liangaustin/Atmosphere/demo1/media/1786612738577.jpg

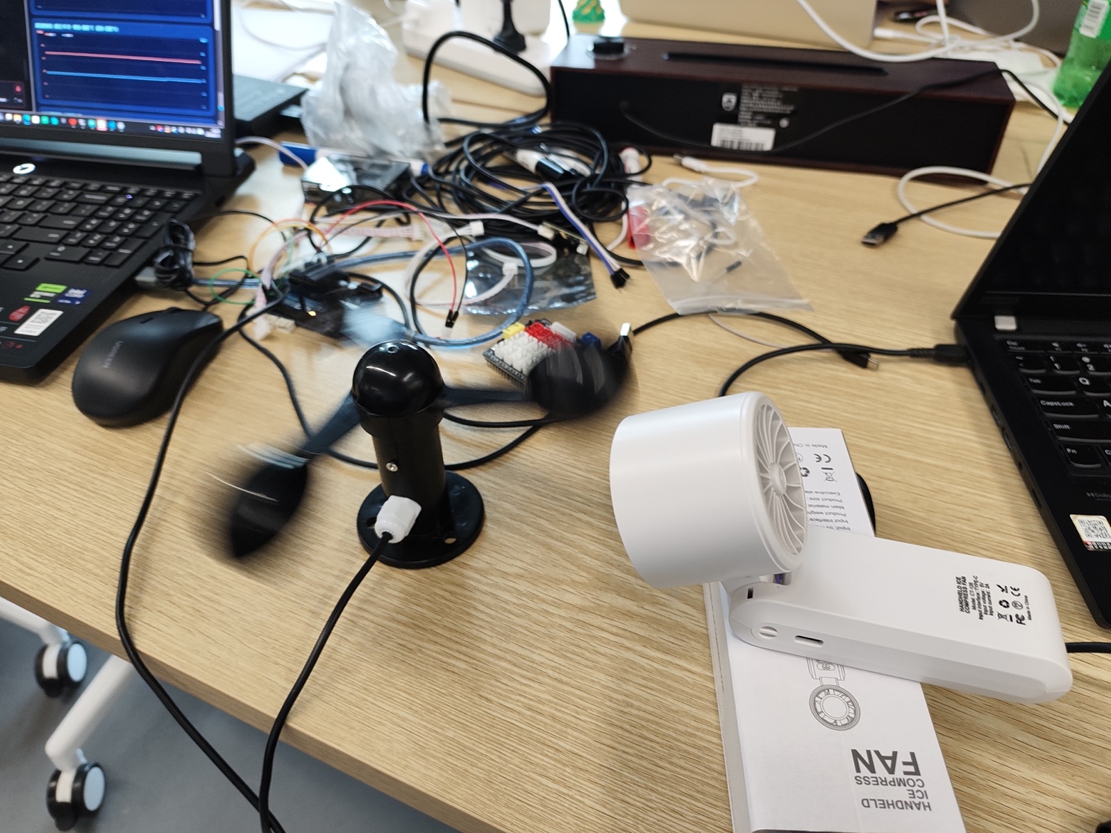
demo1/media/1786612738577.jpg
