liangaustin/Atmosphere/demo1/media/1786612738665.jpg

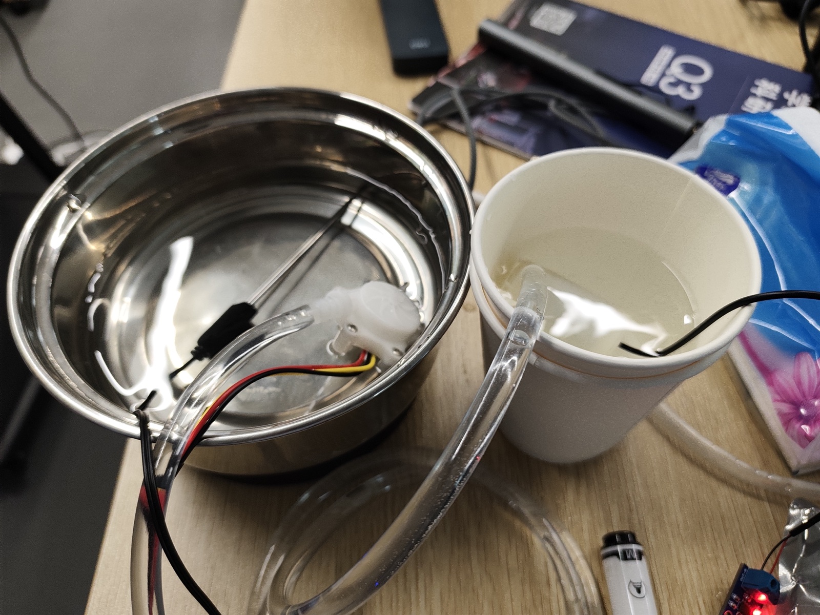
demo1/media/1786612738665.jpg
