liangaustin/Atmosphere/demo1/media/1786612738705.jpg

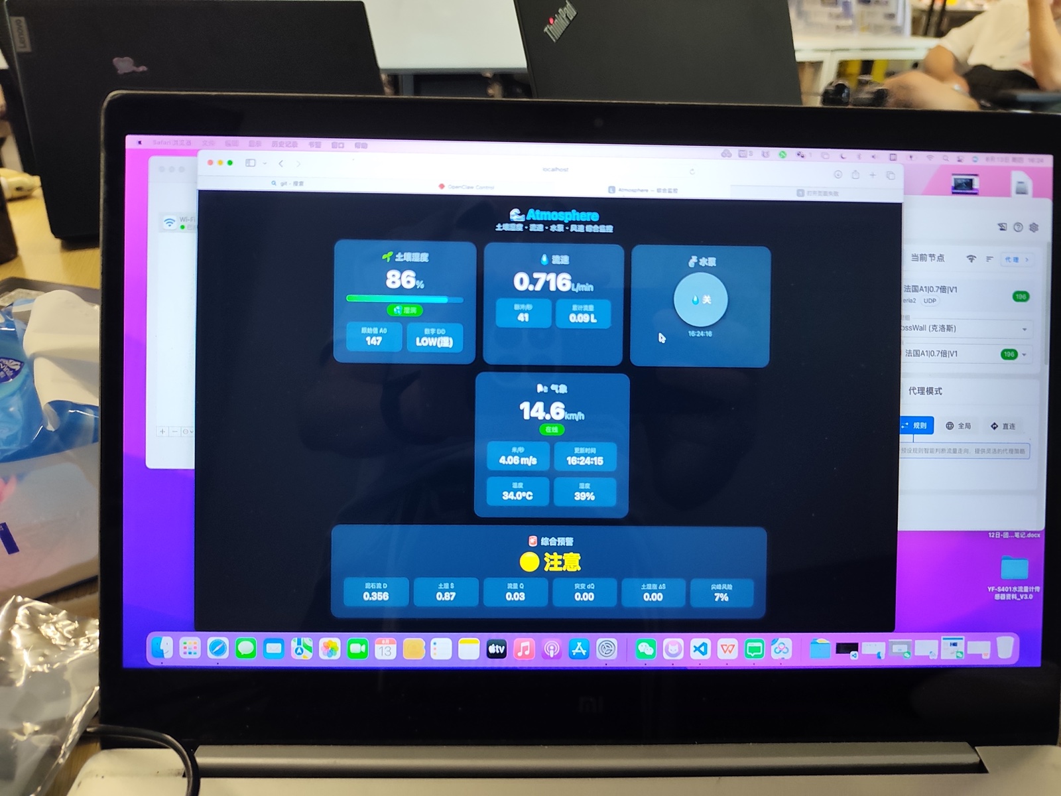
demo1/media/1786612738705.jpg
