liangaustin/Atmosphere/demo1/zh-CN/第二版算法部分/beta5/server.py

#!/usr/bin/env python3
"""Atmosphere - 综合监控：土壤湿度 + 流速 + 水泵控制"""
import json, time, http.server, threading, sys
import urllib.request
from collections import deque
import serial

SERIAL_PORT = "/dev/cu.usbserial-14120"
WIND_URL = "http://192.168.1.200:8001/wind"
WEB_PORT = 8080
latest = {
    "pump": 0, "soil_raw": 0, "soil_percent": -1, "soil_dry": False,
    "soil_connected": True, "flow_pulses": 0, "flow": 0.0, "total": 0.0,
    "wind_ms": 0.0, "wind_kmh": 0.0, "wind_time": "", "wind_connected": False,
    "temp": 0.0, "hum": 0.0, "dht_ok": False,
    "time": ""
}

ser = None
serial_lock = threading.Lock()

def read_serial():
    global latest, ser
    while True:
        try:
            with serial_lock:
                ser = serial.Serial(SERIAL_PORT, 115200, timeout=0.5)
                # 禁用 DTR/RTS，避免串口开关时触发 Arduino 自动复位
                ser.dtr = False
                ser.rts = False
            time.sleep(0.5)
            print(f"✅ 串口已连接: {SERIAL_PORT}", flush=True)
            last_read = time.time()
            while True:
                with serial_lock:
                    if ser is None:
                        raise TimeoutError("serial closed")
                    line = ser.readline()
                if line:
                    try:
                        data = json.loads(line.decode(errors='ignore').strip())
                        data["time"] = time.strftime("%H:%M:%S")
                        latest.update(data)
                        last_read = time.time()
                    except json.JSONDecodeError:
                        pass
                else:
                    # readline 超时返回空 → 累计 30 秒无数据才重连（减少复位频率）
                    if time.time() - last_read > 30:
                        print("⚠️ 30秒无数据，强制重连串口", flush=True)
                        raise TimeoutError("serial idle timeout")
        except Exception as e:
            print(f"❌ 串口错误，5秒后重连: {e}", flush=True)
            try:
                with serial_lock:
                    if ser:
                        ser.close()
            except Exception:
                pass
            ser = None
            time.sleep(5)

def lcd_sender():
    """每秒向 Arduino 下发 LCD 显示数据：D<风速km/h>,<预警等级>\n"""
    while True:
        try:
            with serial_lock:
                if ser is not None:
                    w = latest.get("wind_kmh", 0.0) or 0.0
                    lv = model.get("final_lv", 0)
                    ser.write(("D%.1f,%d\n" % (w, lv)).encode())
                    ser.flush()
        except Exception:
            pass
        time.sleep(1)

def fetch_wind():
    global latest
    last_ok = [0.0]
    while True:
        try:
            req = urllib.request.Request(WIND_URL, headers={'User-Agent': 'curl/7.64'})
            with urllib.request.urlopen(req, timeout=5) as r:
                d = json.loads(r.read().decode())
                latest["wind_ms"] = d.get("wind_ms", 0.0)
                latest["wind_kmh"] = d.get("wind_kmh", 0.0)
                latest["wind_time"] = d.get("time", "")
                # 温湿度：本地 DHT11 优先，无本地数据才用风速电脑的
                if not latest.get("dht_ok", False):
                    latest["temp"] = d.get("temp", 0.0)
                    latest["hum"] = d.get("hum", 0.0)
                last_ok[0] = time.time()
        except Exception:
            pass
        # 10 秒内有成功就算在线（容错对方时通时断）
        latest["wind_connected"] = (time.time() - last_ok[0]) < 10
        time.sleep(1)

# ══════════ 预警模型 ══════════
# 预警档位：0 正常 / 1 一级预警 / 2 二级预警 / 3 三级预警（三级最严重）
LV_TEXT = ["🟢 正常", "🟡 一级预警", "🟠 二级预警", "🔴 三级预警"]

# 泥石流模型标定参数（v2：对齐 YF-S401 实测量程）
Q_MAX = 3.0    # 满槽流量 L/min（实测新泵最大 ~1.7，留余量 3）
DQ_MAX = 0.5   # 流量变化率上限 L/min/s（实测秒级跳变 ~0.3）
DS_MAX = 15.0  # 土壤10分钟变化上限 %

flow_hist = deque(maxlen=300)   # 5分钟流量历史（每秒一点）
soil_hist = deque(maxlen=600)   # 10分钟湿度历史（每秒一点）
wind_hist = deque(maxlen=300)   # 5分钟风速历史（每秒一点）
hist_lock = threading.Lock()

# ── 滑动基准（24小时窗口，每分钟一点，自适应地区气候）──
BASE_LEN = 1440        # 24h × 60min
BASE_MIN = 15          # 收集 15 分钟数据即启用滑动基准（v2 调整：120→15，更快自适应）
flow_base = deque(maxlen=BASE_LEN)
soil_base = deque(maxlen=BASE_LEN)
spike_base = deque(maxlen=BASE_LEN)   # 尖峰基准（流量秒级变化率）
base_last = [0.0]      # 上次基准采样时间

def pct(data, p):
    """排序后取第 p 百分位（0-100）"""
    if not data:
        return None
    s = sorted(data)
    idx = int(len(s) * p / 100.0)
    idx = max(0, min(len(s) - 1, idx))
    return s[idx]

def sliding_norm(v, base):
    """把当前值映射到该地 [P10, P95] 区间的 0~1 相对偏离；数据不足返回 None"""
    if len(base) < BASE_MIN:
        return None
    p10 = pct(base, 10)
    p95 = pct(base, 95)
    if p95 - p10 < 1e-6:
        return None
    return max(0.0, min(1.0, (v - p10) / (p95 - p10)))

# 滞回保持：各等级最短保持秒数（防抖，避免预警闪一下就恢复）
HOLD_SEC = {1: 10, 2: 15, 3: 20}
_lv_hold_until = [0.0, 0.0, 0.0, 0.0]
_cur_lv = [0]

model = {
    "debris_D": 0.0, "debris_lv": 0, "debris_lv_text": LV_TEXT[0],
    "Sn": 0.0, "Qn": 0.0, "dQn": 0.0, "dSn": 0.0,
    "spike": 0.0, "spike_risk": 0.0,
    "final_lv": 0, "final_lv_text": LV_TEXT[0],
}

def rising_5min():
    """流量是否连续5分钟上升（5段60秒窗口，≥4段上升判定为持续上涨）"""
    if len(flow_hist) < 300:
        return False
    seg = []
    for i in range(5):
        vals = [flow_hist[j][1] for j in range(-300 + i * 60, -240 + i * 60)]
        seg.append(sum(vals) / 60.0)
    up = sum(1 for i in range(4) if seg[i + 1] > seg[i])
    return up >= 4

def model_loop():
    global model
    while True:
        try:
            with hist_lock:
                t = time.time()
                flow = latest.get("flow", 0.0)
                soil = latest.get("soil_percent", -1)
                if soil < 0:
                    soil = 0
                flow_hist.append((t, flow))
                soil_hist.append((t, soil))
                wind_hist.append((t, latest.get("wind_kmh", 0.0)))

                # 每分钟采样到 24h 滑动基准窗口
                if t - base_last[0] >= 60:
                    base_last[0] = t
                    flow_base.append(flow)
                    soil_base.append(soil)
                    _spk = flow_hist[-1][1] - flow_hist[-2][1] if len(flow_hist) >= 2 else 0.0
                    spike_base.append(max(0.0, _spk))

                # ── 泥石流四因子归一化（滑动基准自适应，数据不足回退绝对值）──
                Sn = sliding_norm(soil, soil_base)
                if Sn is None:
                    Sn = soil / 100.0
                Qn = sliding_norm(flow, flow_base)
                if Qn is None:
                    Qn = min(flow / Q_MAX, 1.0)
                dq = (flow_hist[-1][1] - flow_hist[-60][1]) / 60.0 if len(flow_hist) >= 60 else 0.0
                dqn = min(abs(dq) / DQ_MAX, 1.0)
                ds = 0.0
                if len(soil_hist) >= 600:
                    ds = soil_hist[-1][1] - soil_hist[-600][1]
                    if ds < 0:
                        ds = 0
                dsn = min(ds / DS_MAX, 1.0)

                # 综合危险指数 D = 0.30S̄ + 0.35Q̄ + 0.20(dQ/dt)̄ + 0.15(ΔS)̄
                # v1 调整：土壤 0.40→0.30（土湿易饱和顶分），流量升为最高权重（山洪更关键）
                D = 0.30 * Sn + 0.35 * Qn + 0.20 * dqn + 0.15 * dsn

                # ── 山洪路径（独立于土壤门槛：流量水平 + 流量突变）──
                # F = 0.6Q̄ + 0.4dQ̄，模拟曼宁公式缺水位时的流量近似
                F = 0.6 * Qn + 0.4 * dqn
                flood_lv = 0
                if F >= 0.75: flood_lv = 3
                elif F >= 0.55: flood_lv = 2
                elif F >= 0.45: flood_lv = 1

                # ── 泥石流分级（特殊规则优先）──
                # 土壤"高湿"判定：优先滑动基准 P90，数据不足回退绝对 60%
                _sp90 = pct(soil_base, 90)
                soil_high = (soil > _sp90) if _sp90 is not None else (soil >= 60)

                debris_lv = 0
                # 门槛：土壤未饱和（<60%）时泥石流起不来，直接安全，不参与 D 分级
                if soil >= 60:
                    if soil_high and dq > 0 and rising_5min():
                        debris_lv = 3
                    elif soil_high and Qn >= 0.70:
                        debris_lv = 2
                    if ds >= 20 and debris_lv < 1:
                        debris_lv = 1
                    if debris_lv == 0:
                        if D >= 0.75:
                            debris_lv = 3
                        elif D >= 0.55:
                            debris_lv = 2
                        elif D >= 0.45:   # 0.30→0.45，土壤湿度单独(≤0.40)不再触发三级
                            debris_lv = 1

                # ── 山洪尖峰（30%分量，用流量秒级变化率近似；曼宁需水位暂缺）──
                spike = max(0.0, flow_hist[-1][1] - flow_hist[-2][1]) if len(flow_hist) >= 2 else 0.0
                # 尖峰按滑动基准自适应：对比当地历史流量变化率分布，超 P95 才算高风险
                spike_risk = sliding_norm(spike, spike_base)
                if spike_risk is None:
                    spike_risk = min(spike / 0.5, 1.0)  # 基准不足回退：实测秒级变化率 ~0.3，0.5 为高值

                # ── 风速风险（独立因子；强风 = 强对流前兆，山洪诱因）──
                w = latest.get("wind_kmh", 0.0)
                wind_risk = min(w / 40.0, 1.0)
                wind_lv = 0
                if w >= 60: wind_lv = 3
                elif w >= 40: wind_lv = 2
                elif w >= 25: wind_lv = 1
                # 风速突变：60 秒内涨 ≥12 km/h → 升一级
                wind_surge = len(wind_hist) >= 60 and (w - wind_hist[-60][1]) >= 12
                # 土壤秒级突变：5 秒内涨 ≥20% → 一级（饱和渗流信号）
                soil_surge = len(soil_hist) >= 5 and (soil - soil_hist[-5][1]) >= 20
                # 流量尖峰等级（spike_risk 满 1.0 = 超当地 P95）
                spike_lv = 0
                if spike_risk >= 1.0: spike_lv = 2
                elif spike_risk >= 0.8: spike_lv = 1
                # 突变合并
                surge_lv = 1 if (wind_surge or soil_surge) else 0

                # 土壤持续高饱和：≥85% 或超当地 P90 → 至少一级（不依赖流量，土体饱和本身就是危险）
                soil_sat_lv = 1 if (soil >= 85 or (_sp90 is not None and soil > _sp90)) else 0

                # 最终等级 = 各因子取最高（泥石流 / 山洪 / 风速 / 尖峰 / 突变 / 土壤饱和）
                final_raw = max(debris_lv, flood_lv, wind_lv, spike_lv, surge_lv, soil_sat_lv)
                # 滞回：升级立即生效并保持；降级需超过保持时间
                tnow = time.time()
                if final_raw >= _cur_lv[0]:
                    _cur_lv[0] = final_raw
                    _lv_hold_until[final_raw] = tnow + HOLD_SEC.get(final_raw, 10)
                elif tnow >= _lv_hold_until[_cur_lv[0]]:
                    _cur_lv[0] = final_raw
                final_lv = _cur_lv[0]

                model.update({
                    "debris_D": round(D, 3), "debris_lv": debris_lv,
                    "debris_lv_text": LV_TEXT[debris_lv],
                    "flood_F": round(F, 3), "flood_lv": flood_lv,
                    "Sn": round(Sn, 3), "Qn": round(Qn, 3),
                    "dQn": round(dqn, 3), "dSn": round(dsn, 3),
                    "spike": round(spike, 3), "spike_risk": round(spike_risk, 3),
                    "wind_risk": round(wind_risk, 3), "wind_lv": wind_lv,
                    "final_lv": final_lv, "final_lv_text": LV_TEXT[final_lv],
                    "baseline_ready": len(soil_base) >= BASE_MIN,
                    "soil_p90": round(_sp90, 1) if _sp90 is not None else -1,
                })
        except Exception as e:
            print(f"模型计算错误: {e}", flush=True)
        time.sleep(1)

HTML = """<!DOCTYPE html>
<html lang="zh-CN">
<head>
<meta charset="UTF-8">
<meta name="viewport" content="width=device-width, initial-scale=1.0">
<title>Atmosphere — 综合监控</title>
<style>
*{margin:0;padding:0;box-sizing:border-box}
body{font-family:-apple-system,system-ui,sans-serif;background:#0b1218;color:#e0e0e0;
  min-height:100vh;padding:24px;display:flex;flex-direction:column;align-items:center}
h1{font-size:1.6em;color:#4fc3f7;margin-bottom:4px}
.sub{color:#78909c;margin-bottom:24px;font-size:.85em}
.grid{display:flex;gap:16px;flex-wrap:wrap;justify-content:space-evenly;max-width:1200px;width:100%;margin-bottom:20px}
.card.full{flex-basis:100%;max-width:100%}
.card{background:#1a2a36;border-radius:18px;padding:18px 20px;flex:1;min-width:230px;max-width:270px;text-align:center}
.card h2{font-size:.95em;color:#90a4ae;font-weight:600;margin-bottom:12px;letter-spacing:.5px}
.big{font-size:2.2em;font-weight:800;line-height:1;margin:6px 0}
.unit{font-size:.4em;color:#78909c;font-weight:400}
/* 湿度进度条 */
.bar{height:10px;background:#1e3a4a;border-radius:6px;overflow:hidden;margin:14px 0 6px}
.bar .fill{height:100%;background:linear-gradient(90deg,#43a047,#4fc3f7);border-radius:6px;transition:width .4s}
.tag{font-size:.8em;padding:4px 12px;border-radius:14px;display:inline-block}
.tag.wet{background:#1b5e20;color:#81c784}
.tag.dry{background:#5d4037;color:#ffab91}
.tag.disconn{background:#b71c1c;color:#ffcdd2}
/* 水泵开关 */
.switch{width:92px;height:92px;border-radius:50%;border:none;font-size:.95em;font-weight:700;
  cursor:pointer;margin:8px auto 6px;display:block;transition:all .2s;color:#fff}
.switch.off{background:#455a64;box-shadow:0 4px 12px rgba(0,0,0,.4)}
.switch.on{background:#2e7d32;box-shadow:0 4px 20px rgba(46,125,50,.6)}
.switch:active{transform:scale(.94)}
/* 曲线区 */
.legend{display:flex;gap:16px;justify-content:center;font-size:.75em;color:#90a4ae;margin-top:6px;flex-wrap:wrap}
.legend span{display:inline-flex;align-items:center;gap:5px}
.legend b{color:#e0e0e0}
.dot{width:12px;height:3px;border-radius:2px;display:inline-block}
canvas{width:100%;display:block;aspect-ratio:14/3}
.row{display:flex;gap:10px;margin-top:14px}
.mini{flex:1;background:#1e3a4a;border-radius:10px;padding:10px}
.mini .lb{font-size:.68em;color:#78909c}
.mini .vl{font-size:1.15em;font-weight:600;margin-top:4px}
.time{color:#546e7a;font-size:.75em;margin-top:20px}
</style>
</head>
<body>
<h1>🌊 Atmosphere</h1>
<div class="sub">土壤湿度 · 流速 · 水泵 · 风速 综合监控</div>

<div class="grid">
  <!-- 土壤湿度卡片 -->
  <div class="card">
    <h2>🌱 土壤湿度</h2>
    <div class="big"><span id="soil">--</span><span class="unit">%</span></div>
    <div class="bar"><div class="fill" id="soilBar" style="width:0%"></div></div>
    <span class="tag disconn" id="soilTag">--</span>
    <div class="row">
      <div class="mini"><div class="lb">原始值 A0</div><div class="vl" id="soilRaw">--</div></div>
      <div class="mini"><div class="lb">数字 DO</div><div class="vl" id="soilDO">--</div></div>
    </div>
  </div>

  <!-- 流速卡片 -->
  <div class="card">
    <h2>💧 流速</h2>
    <div class="big"><span id="flow">0.000</span><span class="unit">L/min</span></div>
    <div class="row">
      <div class="mini"><div class="lb">脉冲/秒</div><div class="vl" id="pulses">--</div></div>
      <div class="mini"><div class="lb">累计流量</div><div class="vl" id="total">--</div></div>
    </div>
  </div>

  <!-- 水泵卡片 -->
  <div class="card">
    <h2>🚰 水泵</h2>
    <button class="switch off" id="pumpBtn">💧 关</button>
    <div class="row" style="margin-top:14px">
      <div class="mini" style="flex:1"><div class="lb">速度</div><div class="vl" id="speedLbl">0%</div></div>
      <div class="mini" style="flex:1"><div class="lb">整机功率</div><div class="vl" id="powerLbl">0.40 W</div></div>
    </div>
    <input type="range" id="speedSlider" min="0" max="100" value="0"
      style="width:100%;margin-top:12px;accent-color:#2e7d32">
    <div class="time" id="time" style="margin-top:8px">--</div>
  </div>
  <!-- 气象卡片 -->
  <div class="card">
    <h2>🌬️ 气象</h2>
    <div class="big"><span id="wind">--</span><span class="unit">km/h</span></div>
    <span class="tag disconn" id="windTag">--</span>
    <div class="row">
      <div class="mini"><div class="lb">米/秒</div><div class="vl" id="windMs">--</div></div>
      <div class="mini"><div class="lb">更新时间</div><div class="vl" id="windTime">--</div></div>
    </div>
    <div class="row">
      <div class="mini"><div class="lb">温度</div><div class="vl" id="tempV">--</div></div>
      <div class="mini"><div class="lb">湿度</div><div class="vl" id="humV">--</div></div>
    </div>
  </div>
</div>

<div class="grid">
  <!-- 曲线卡片 -->
  <div class="card full">
    <h2>📈 实时曲线（温度 · 湿度 · 风速）</h2>
    <canvas id="mainChart"></canvas>
    <div class="legend"><span><i class="dot" style="background:#ef5350"></i>温度 <b id="curTemp">--</b>℃</span><span><i class="dot" style="background:#42a5f5"></i>湿度 <b id="curHum">--</b>%</span><span><i class="dot" style="background:#66bb6a"></i>风速 <b id="curWind">--</b>km/h</span></div>
  </div>
</div>

<div class="grid">
  <!-- 预警卡片 -->
  <div class="card full">
    <h2>🚨 综合预警</h2>
    <div class="big" id="alertLv" style="font-size:1.8em">--</div>
    <div class="row" style="flex-wrap:wrap;justify-content:center">
      <div class="mini"><div class="lb">泥石流 D</div><div class="vl" id="debrisD">--</div></div>
      <div class="mini"><div class="lb">土湿 S̄</div><div class="vl" id="fSn">--</div></div>
      <div class="mini"><div class="lb">流量 Q̄</div><div class="vl" id="fQn">--</div></div>
      <div class="mini"><div class="lb">突变 dQ̄</div><div class="vl" id="fdQn">--</div></div>
      <div class="mini"><div class="lb">土湿涨 ΔS̄</div><div class="vl" id="fdSn">--</div></div>
      <div class="mini"><div class="lb">尖峰风险</div><div class="vl" id="spikeRisk">--</div></div>
      <div class="mini"><div class="lb">山洪 F</div><div class="vl" id="floodF">--</div></div>
      <div class="mini"><div class="lb">风速风险</div><div class="vl" id="windRisk">--</div></div>
    </div>
  </div>
</div>

<script>
let pumpState = 0;
let pumpSpeedPct = 0;
const MAX_POINTS = 600;   // 5 分钟曲线（500ms 一点）
let history = [];

function drawLineChart(canvas, series){
  const dpr = window.devicePixelRatio || 1;
  const w = canvas.clientWidth, h = canvas.clientHeight;
  if(!w || !h) return;
  canvas.width = w * dpr; canvas.height = h * dpr;
  const ctx = canvas.getContext('2d');
  ctx.setTransform(dpr, 0, 0, dpr, 0, 0);
  ctx.clearRect(0, 0, w, h);
  const padL = 34, padR = 34, padT = 8, padB = 16;
  const gw = w - padL - padR, gh = h - padT - padB;
  // 网格 + 刻度（left 系列左轴，right 系列右轴）
  ctx.strokeStyle = '#1e3a4a'; ctx.lineWidth = 1;
  ctx.fillStyle = '#78909c'; ctx.font = '9px sans-serif';
  for(let i = 0; i <= 4; i++){
    const y = padT + gh * i / 4;
    ctx.beginPath(); ctx.moveTo(padL, y); ctx.lineTo(w - padR, y); ctx.stroke();
    const left = series.find(s => s.side === 'left'), right = series.find(s => s.side === 'right');
    if(left){
      ctx.textAlign = 'right';
      const v = left.yMax - (left.yMax - left.yMin) * i / 4;
      ctx.fillText(v.toFixed(1), padL - 4, y + 3);
    }
    if(right){
      ctx.textAlign = 'left';
      const v = right.yMax - (right.yMax - right.yMin) * i / 4;
      ctx.fillText(v.toFixed(0), w - padR + 4, y + 3);
    }
  }
  // 右侧时间
  ctx.textAlign = 'right'; ctx.fillStyle = '#546e7a';
  const now = new Date();
  const ts = [now.getHours(), now.getMinutes(), now.getSeconds()].map(x => String(x).padStart(2, '0')).join(':');
  ctx.fillText(ts, w - 2, h - 2);
  // 曲线（数据不满 600 点时拉伸铺满全宽；满后固定窗口滚动）
  for(const s of series){
    ctx.strokeStyle = s.color; ctx.lineWidth = 1.8;
    ctx.beginPath(); let started = false;
    const n = s.data.length;
    for(let i = 0; i < n; i++){
      const v = s.data[i];
      if(v === null || v === undefined){ started = false; continue; }
      let x;
      if(n <= MAX_POINTS){
        x = padL + gw * (n > 1 ? i / (n - 1) : 0);        // 数据少 → 铺满
      } else {
        x = padL + gw * (i - (n - MAX_POINTS)) / (MAX_POINTS - 1);  // 满窗 → 滚动
      }
      const y = padT + gh * (1 - (v - s.yMin) / (s.yMax - s.yMin));
      if(!started){ ctx.moveTo(x, y); started = true; }
      else ctx.lineTo(x, y);
    }
    ctx.stroke();
  }
}

function drawCharts(){
  const temps = history.map(p => p.temp), hums = history.map(p => p.hum), winds = history.map(p => p.wind);
  // 温度动态范围（左轴）
  const tvals = temps.filter(v => v !== null && v !== undefined);
  let tMin = 15, tMax = 35;
  if(tvals.length){ tMin = Math.min(...tvals); tMax = Math.max(...tvals); }
  tMin -= 2; tMax += 2;
  if(tMax - tMin < 4) tMax = tMin + 4;
  // 风速动态范围（自身归一化，无刻度）
  const wvals = winds.filter(v => v !== null && v !== undefined);
  let wMax = 20;
  if(wvals.length) wMax = Math.max(wMax, Math.ceil(Math.max(...wvals) * 1.2 / 10) * 10);
  drawLineChart(document.getElementById('mainChart'), [
    {data: temps, color: '#ef5350', yMin: tMin, yMax: tMax, side: 'left'},
    {data: hums,  color: '#42a5f5', yMin: 0, yMax: 100,  side: 'right'},
    {data: winds, color: '#66bb6a', yMin: 0, yMax: wMax, side: 'none'}
  ]);
}
const PUMP_MAX_WATT = 1.25;   // 水泵满载功率估算（5V×250mA），按铭牌标定可改
const BASE_POWER = 0.4;       // 整机固定功耗估算：Arduino Nano ~0.25W + 土壤湿度 ~0.05W + 流速YF-S401 ~0.1W

async function update(){
  try{
    let r=await fetch('/data');
    let d=await r.json();
    // 土壤湿度
    let soilEl = document.getElementById('soil');
    let tagEl = document.getElementById('soilTag');
    if(!d.soil_connected){
      soilEl.textContent = '--';
      tagEl.textContent = '⚠️ 传感器断线';
      tagEl.className = 'tag disconn';
      document.getElementById('soilBar').style.width = '0%';
    } else {
      let p = d.soil_percent;
      soilEl.textContent = p;
      document.getElementById('soilBar').style.width = p + '%';
      if(d.soil_dry){
        tagEl.textContent = '☀️ 偏干';
        tagEl.className = 'tag dry';
      } else {
        tagEl.textContent = '💦 湿润';
        tagEl.className = 'tag wet';
      }
    }
    document.getElementById('soilRaw').textContent = d.soil_raw;
    document.getElementById('soilDO').textContent = d.soil_dry ? 'HIGH(干)' : 'LOW(湿)';
    // 流速
    document.getElementById('flow').textContent = d.flow.toFixed(3);
    document.getElementById('pulses').textContent = d.flow_pulses;
    document.getElementById('total').textContent = d.total.toFixed(2) + ' L';
    // 水泵
    pumpState = d.pump;
    pumpSpeedPct = Math.round((d.speed ?? 0) / 255 * 100);
    renderPump();
    document.getElementById('time').textContent = d.time;
    // 曲线数据（温湿度 + 风速）
    history.push({
      temp: (d.temp !== null && d.temp !== undefined) ? d.temp : null,
      hum:  (d.hum  !== null && d.hum  !== undefined) ? d.hum  : null,
      wind: d.wind_connected ? (d.wind_kmh ?? 0) : null
    });
    if(history.length > MAX_POINTS) history.shift();
    drawCharts();
    document.getElementById('curTemp').textContent = (d.temp !== null && d.temp !== undefined) ? d.temp.toFixed(1) : '--';
    document.getElementById('curHum').textContent = (d.hum  !== null && d.hum  !== undefined) ? d.hum.toFixed(0) : '--';
    document.getElementById('curWind').textContent = d.wind_connected ? (d.wind_kmh ?? 0).toFixed(1) : '--';
    // 气象（风速+温湿度）
    let windEl = document.getElementById('wind');
    let windTagEl = document.getElementById('windTag');
    if(d.wind_connected){
      windEl.textContent = d.wind_kmh.toFixed(1);
      windTagEl.textContent = '在线';
      windTagEl.className = 'tag wet';
      document.getElementById('windMs').textContent = d.wind_ms.toFixed(2) + ' m/s';
      document.getElementById('windTime').textContent = d.wind_time;
      document.getElementById('tempV').textContent = (d.temp !== null && d.temp !== undefined) ? (d.temp).toFixed(1) + '℃' : '--';
      document.getElementById('humV').textContent = (d.hum !== null && d.hum !== undefined) ? (d.hum).toFixed(0) + '%' : '--';
    } else {
      windEl.textContent = '--';
      windTagEl.textContent = '⚠️ 离线';
      windTagEl.className = 'tag disconn';
      document.getElementById('windMs').textContent = '--';
      document.getElementById('windTime').textContent = '--';
      document.getElementById('tempV').textContent = '--';
      document.getElementById('humV').textContent = '--';
    }
    // 预警
    const lvColors = ['#43a047', '#fdd835', '#fb8c00', '#e53935'];
    let alertEl = document.getElementById('alertLv');
    alertEl.textContent = d.final_lv_text || '--';
    alertEl.style.color = lvColors[d.final_lv] || '#e0e0e0';
    document.getElementById('debrisD').textContent = (d.debris_D ?? 0).toFixed(3);
    document.getElementById('fSn').textContent = (d.Sn ?? 0).toFixed(2);
    document.getElementById('fQn').textContent = (d.Qn ?? 0).toFixed(2);
    document.getElementById('fdQn').textContent = (d.dQn ?? 0).toFixed(2);
    document.getElementById('fdSn').textContent = (d.dSn ?? 0).toFixed(2);
    document.getElementById('spikeRisk').textContent = (((d.spike_risk ?? 0) * 100).toFixed(0)) + '%';
    document.getElementById('floodF').textContent = (d.flood_F ?? 0).toFixed(3);
    document.getElementById('windRisk').textContent = (((d.wind_risk ?? 0) * 100).toFixed(0)) + '%';
  }catch(e){}
}

function renderPump(){
  let btn = document.getElementById('pumpBtn');
  let slider = document.getElementById('speedSlider');
  if(pumpState === 1){
    btn.className = 'switch on';
    btn.textContent = '💧 抽水中';
  } else {
    btn.className = 'switch off';
    btn.textContent = '💧 关';
  }
  document.getElementById('speedLbl').textContent = pumpSpeedPct + '%';
  document.getElementById('powerLbl').textContent = (BASE_POWER + pumpSpeedPct / 100 * PUMP_MAX_WATT).toFixed(2) + ' W';
  if (document.activeElement !== slider) {
    slider.value = pumpSpeedPct;
  }
}

async function togglePump(){
  let v = pumpState === 1 ? 0 : 255;  // 关→0，开→全速255
  try{
    await fetch('/pump?speed=' + v, {method:'POST'});
  }catch(e){}
  // 不手动改状态，等服务器返回真实值（避免竞态回跳）
  setTimeout(update, 150);
}

let lastSpeedSend = 0;
document.getElementById('speedSlider').addEventListener('input', function(){
  let v = parseInt(this.value);
  document.getElementById('speedLbl').textContent = v + '%';
  let now = Date.now();
  if (now - lastSpeedSend > 150) {  // 150ms 防抖，拖动时避免刷屏写串口
    lastSpeedSend = now;
    fetch('/pump?speed=' + Math.round(v * 2.55), {method:'POST'}).catch(()=>{});
  }
});

document.getElementById('pumpBtn').addEventListener('click', togglePump);
setInterval(update, 500);
update();
</script>
</body>
</html>"""

class Handler(http.server.SimpleHTTPRequestHandler):
    def log_message(self, *a):
        pass

    def do_GET(self):
        if self.path == '/data':
            payload = dict(latest)
            payload.update(model)
            self.send_response(200)
            self.send_header('Content-Type', 'application/json')
            self.end_headers()
            self.wfile.write(json.dumps(payload).encode())
        elif self.path in ('/', '/index.html'):
            self.send_response(200)
            self.send_header('Content-Type', 'text/html; charset=utf-8')
            self.end_headers()
            self.wfile.write(HTML.encode())
        else:
            super().do_GET()

    def do_POST(self):
        if self.path.startswith('/pump'):
            import urllib.parse as up
            q = up.parse_qs(up.urlparse(self.path).query)
            cmd = q.get('cmd', [''])[0]
            speed = q.get('speed', [None])[0]
            v = None
            if speed is not None:
                try:
                    v = max(0, min(255, int(speed)))
                except ValueError:
                    v = None
            elif cmd in ('ON', 'OFF'):
                v = 255 if cmd == 'ON' else 0
            if v is not None:
                try:
                    with serial_lock:
                        if ser is not None:
                            ser.write((str(v) + '\n').encode())
                            ser.flush()
                            print(f"📤 已写速度 {v}", flush=True)
                        else:
                            print("⚠️ ser 为 None，命令未发送", flush=True)
                except Exception as e:
                    print(f"写串口错误: {e}", flush=True)
            self.send_response(200)
            self.send_header('Content-Type', 'application/json')
            self.end_headers()
            self.wfile.write(b'{"ok":true}')
        else:
            self.send_response(404)
            self.end_headers()

if __name__ == '__main__':
    threading.Thread(target=read_serial, daemon=True).start()
    threading.Thread(target=lcd_sender, daemon=True).start()
    threading.Thread(target=fetch_wind, daemon=True).start()
    threading.Thread(target=model_loop, daemon=True).start()
    print(f"🌐 http://localhost:{WEB_PORT}")
    http.server.ThreadingHTTPServer(('', WEB_PORT), Handler).serve_forever()
